gagagu/G1000_iPad_Bezel/Stl/Buttons/G1000-07-ButtonsButton_MENU.stl

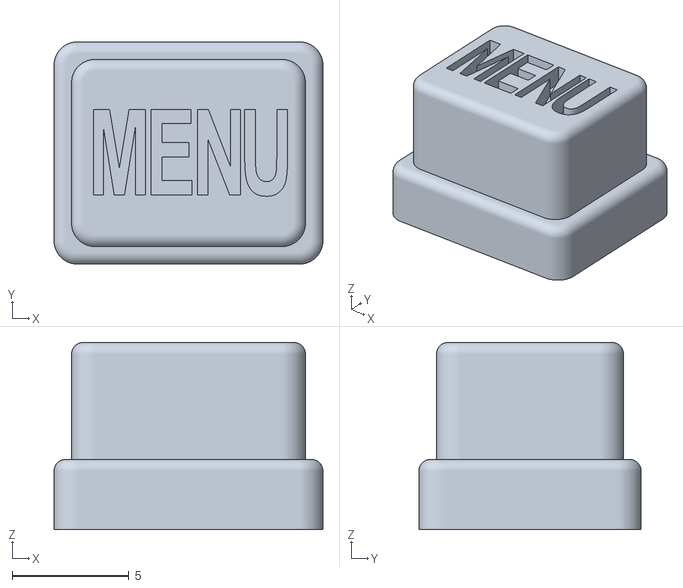
[picture p27: CAD file, 2025-01-13]
Stl/Buttons/G1000-07-ButtonsButton_MENU.stl
11.5 x 9.50 x 8.00
