gagagu/G1000_iPad_Bezel/Gerber-Files/PCB_PCB_G1000_Buttons_Right_2024-04-02.pdf

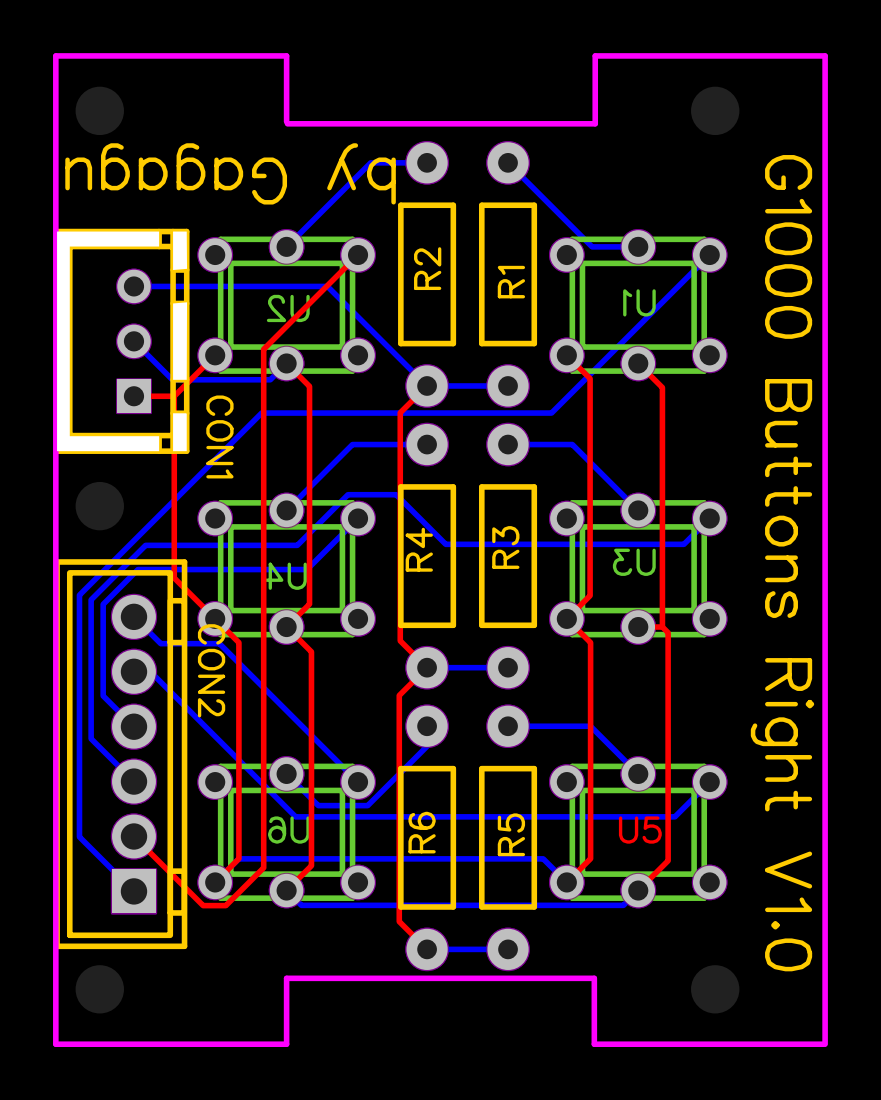
[picture p40: page 1]
