gagagu/G1000_iPad_Bezel/Gerber-Files/PCB_PCB_G1000_Com_Switch_2024-04-02.pdf

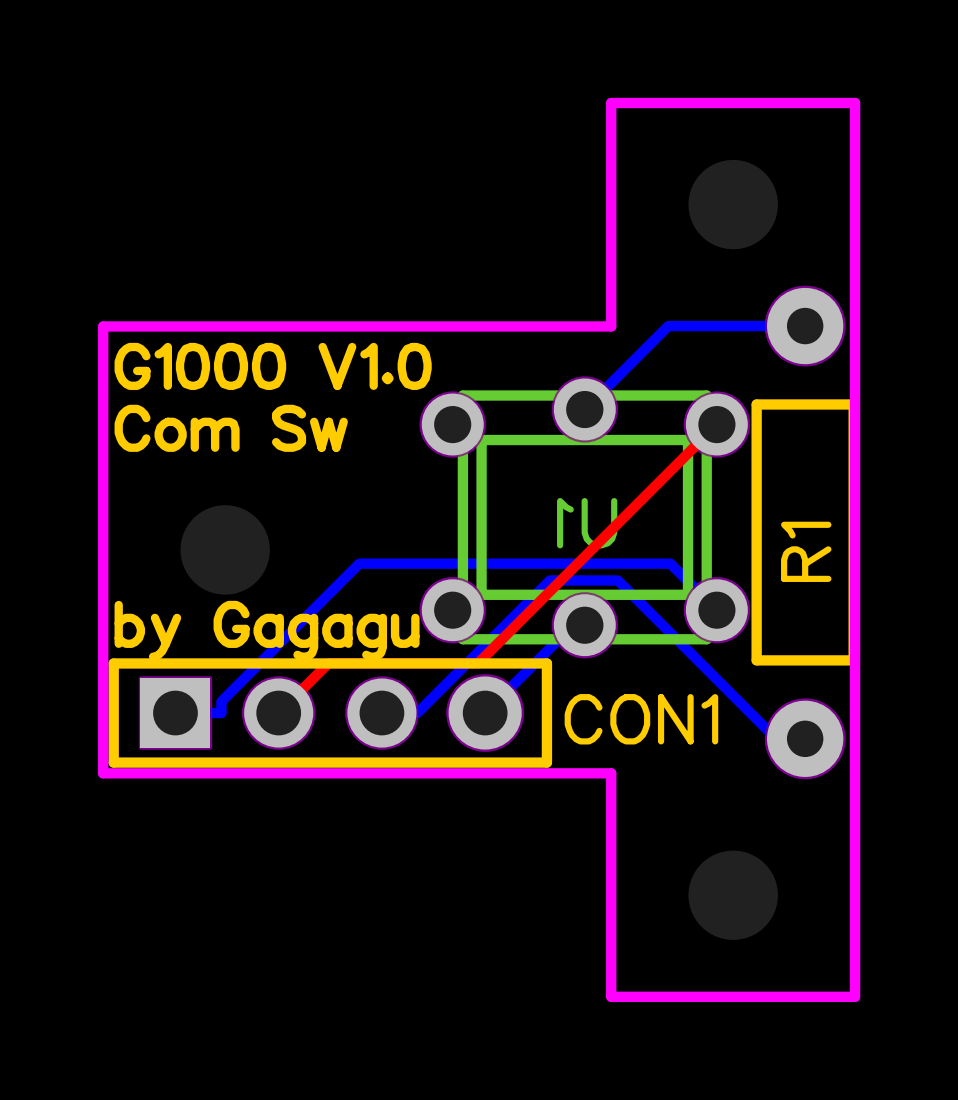
[picture p41: page 1]
