gagagu/G1000_iPad_Bezel/Gerber-Files/PCB_PCB_G1000_Dual_Encoder_Base_2024-04-02.pdf

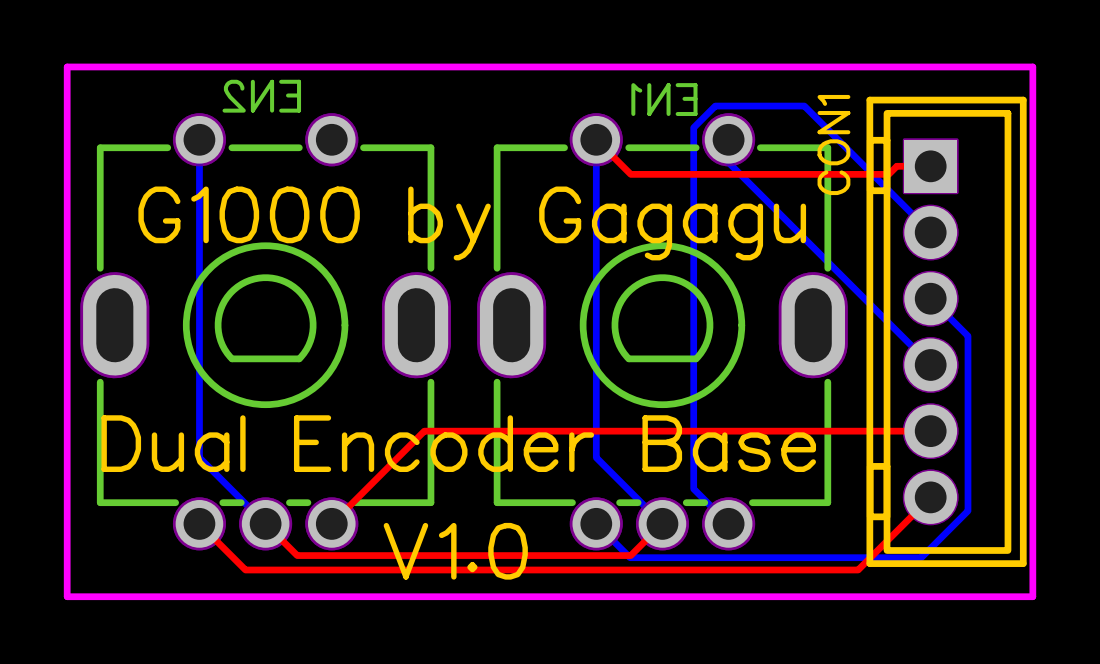
[picture p42: page 1]
