gagagu/G1000_iPad_Bezel/Gerber-Files/PCB_PCB_G1000_Encoder_Base_2024-04-02.pdf

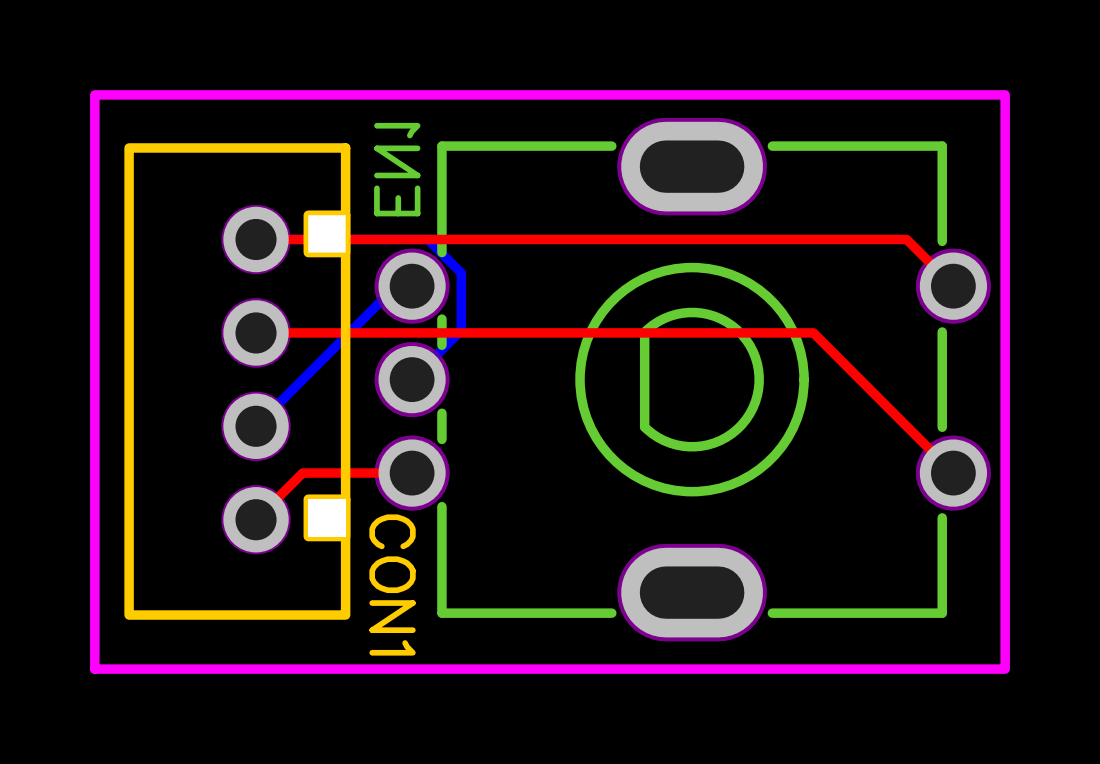
[picture p43: page 1]
