gagagu/G1000_iPad_Bezel/Gerber-Files/PCB_PCB_G1000_Nav_Switch_2024-04-02.pdf

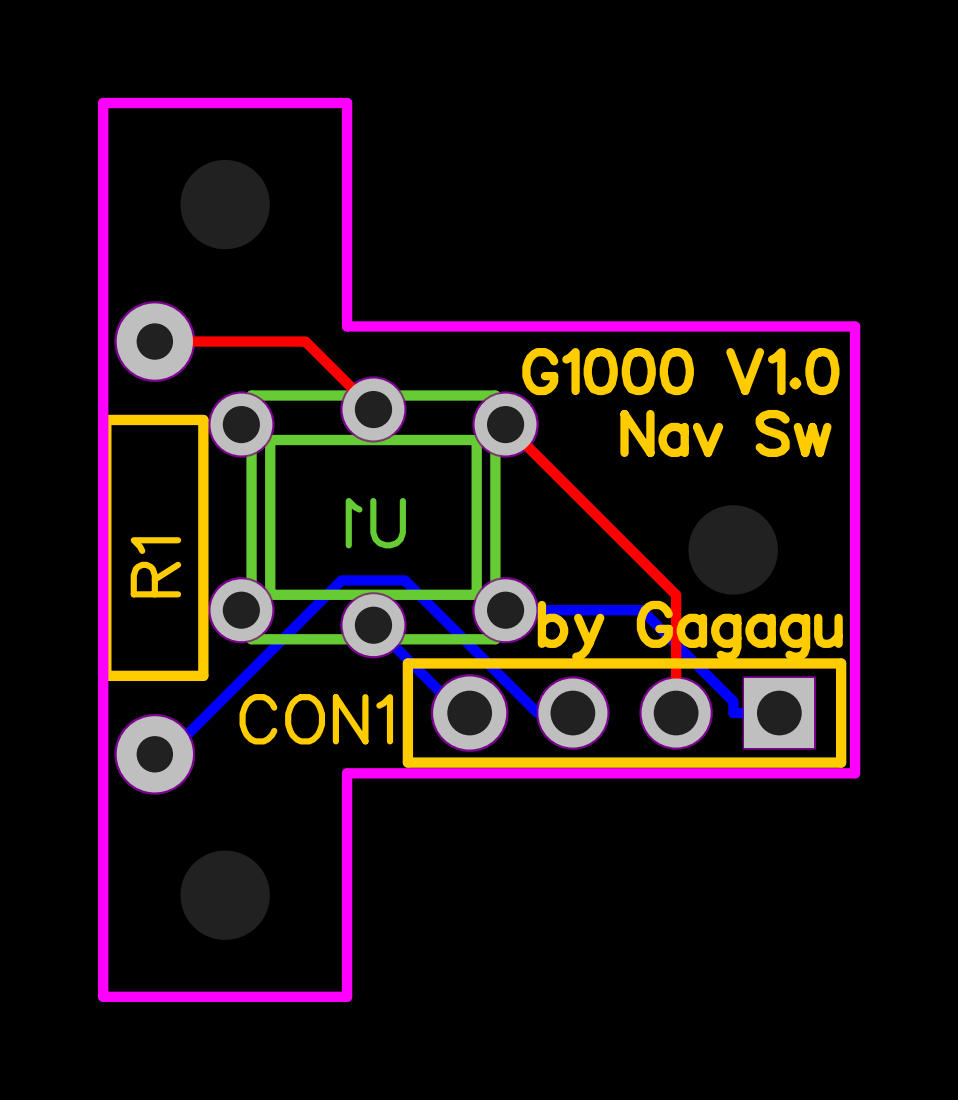
[picture p44: page 1]
