gagagu/G1000_iPad_Bezel/Gerber-Files/PCB_PCB_G1000_Pan_Range_2024-04-02.pdf

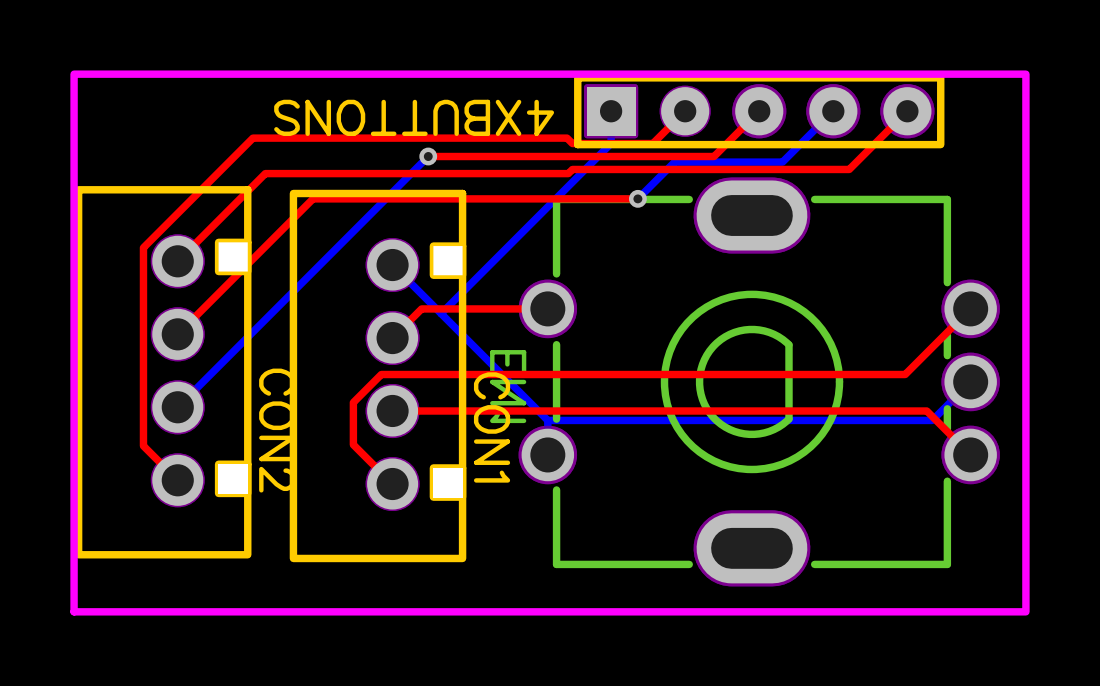
[picture p45: page 1]
